antmicro/framos-csi-adapter/assets/previews/layer0.png

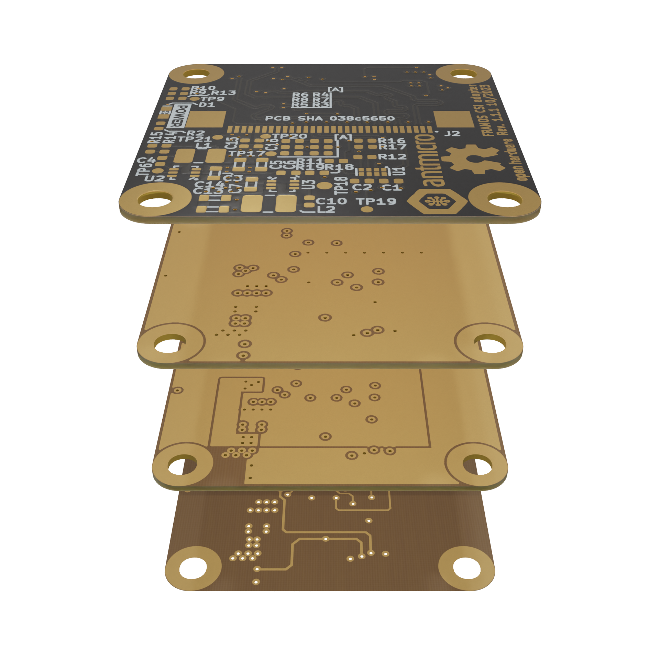
assets/previews/layer0.png
