antmicro/framos-csi-adapter/assets/previews/layer3.png

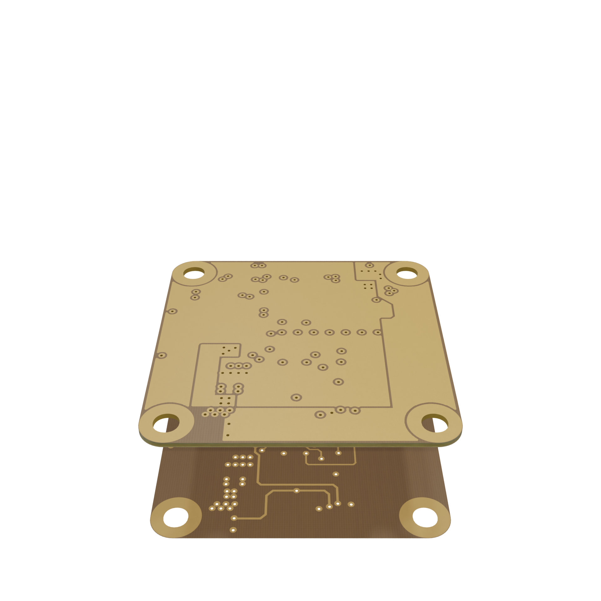
assets/previews/layer3.png
