antmicro/framos-csi-adapter/assets/previews/orthoB.png

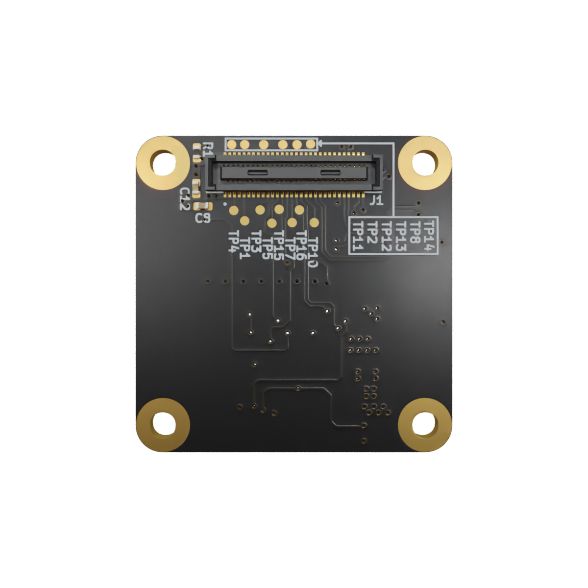
assets/previews/orthoB.png
