antmicro/framos-csi-adapter/assets/previews/orthoT.png

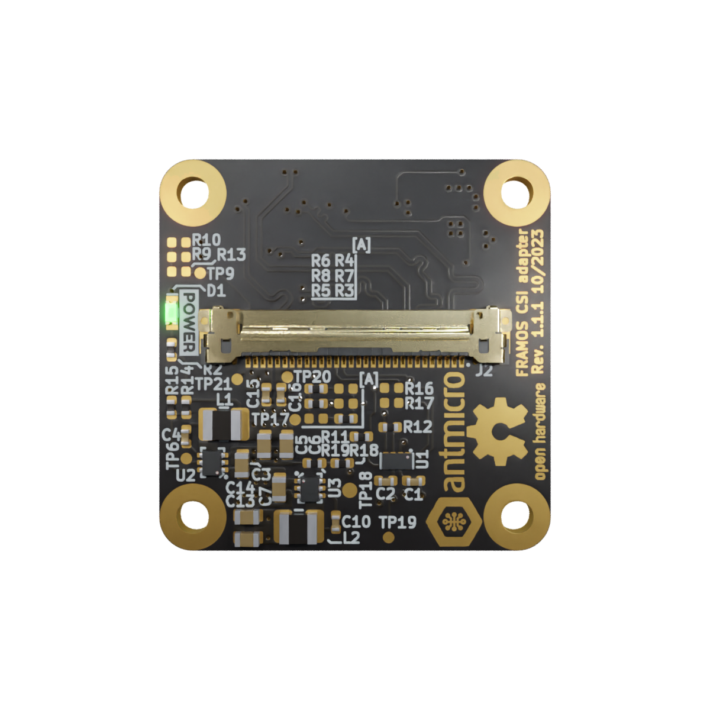
assets/previews/orthoT.png
