antmicro/framos-csi-adapter/assets/previews/photoB.png

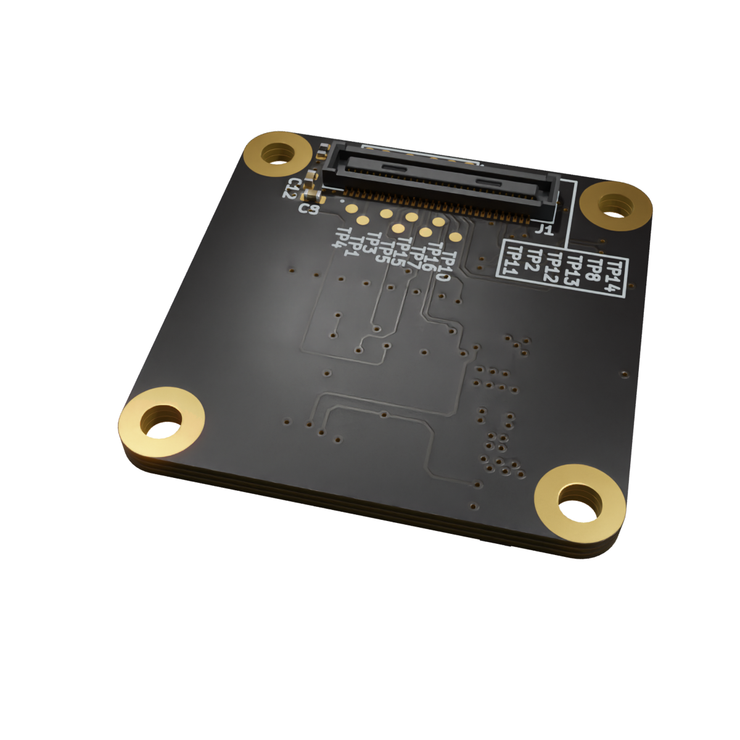
assets/previews/photoB.png
