antmicro/framos-csi-adapter/assets/previews/photoT_thumbnail.png

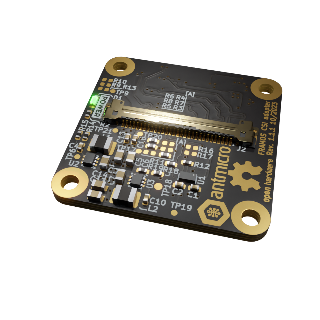
assets/previews/photoT_thumbnail.png
