antmicro/framos-csi-adapter/assets/previews/rightB.png

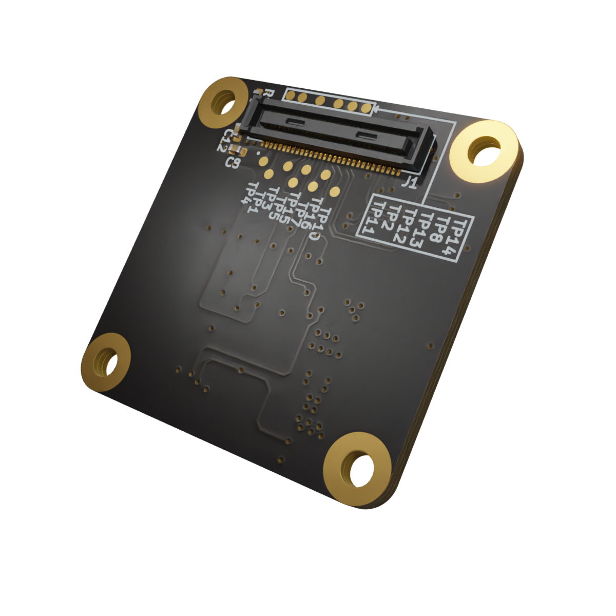
assets/previews/rightB.png
