antmicro/framos-csi-adapter/assets/previews/rightT.png

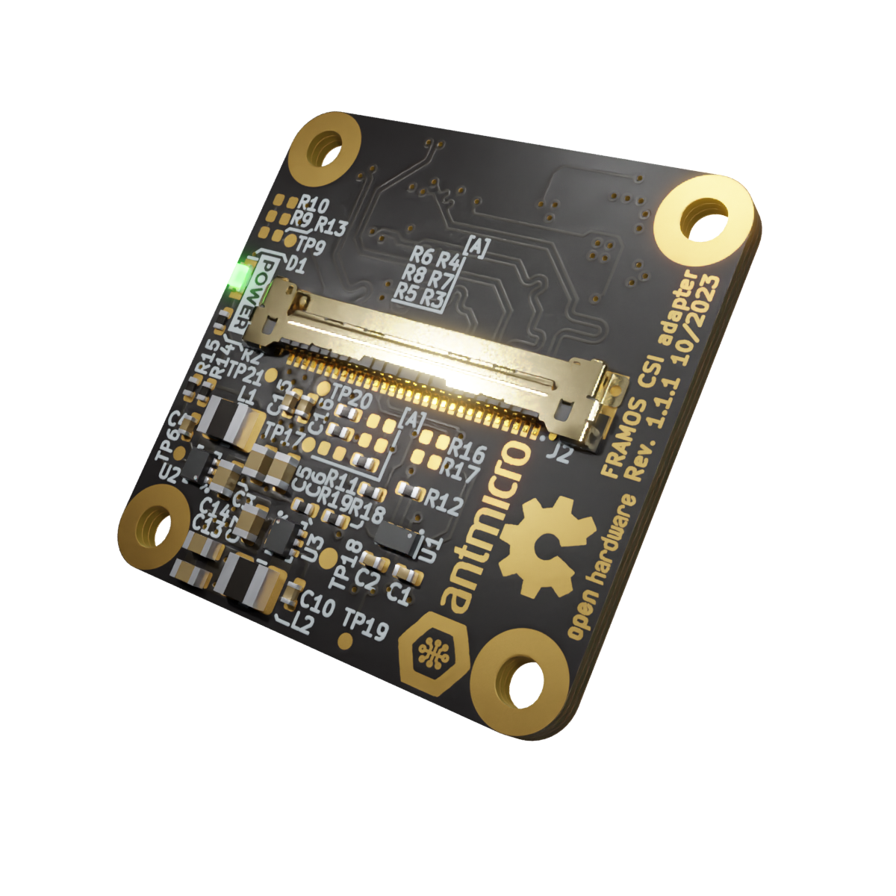
assets/previews/rightT.png
